nickbild/luminaphone/schematic/schematic.kicad_sch

## KiCad design schematic/schematic.kicad_sch (2025-05-27)

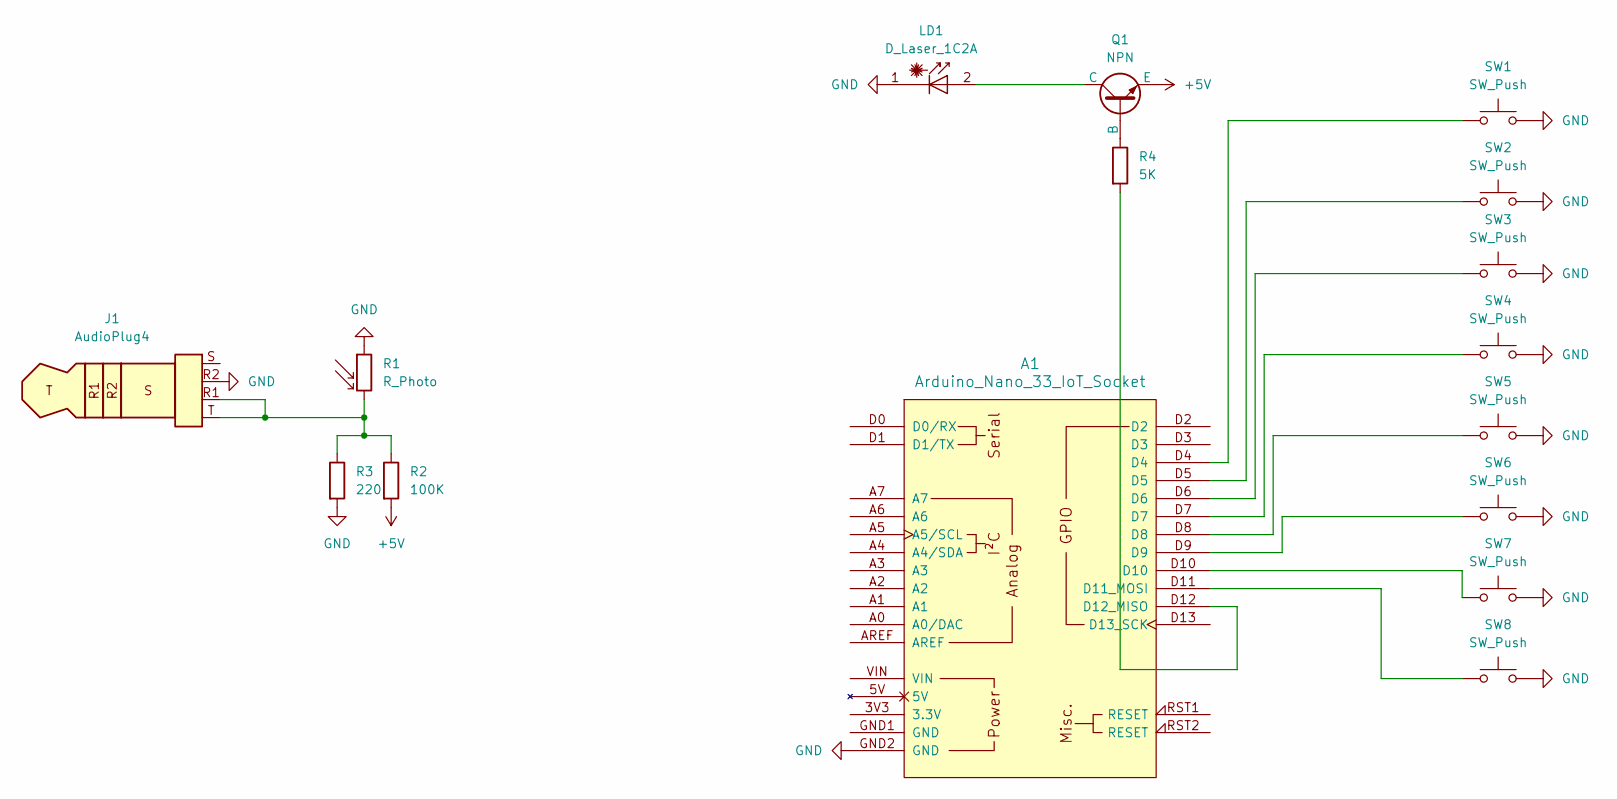
[picture p10: schematic schematic.kicad_sch]

Parts:
A1: Arduino_Nano_33_IoT_Socket
J1: AudioPlug4
LD1: D_Laser_1C2A
Q1: NPN
R1: R_Photo
R2: 100K
R3: 220
R4: 5K
SW1, SW2, SW3, SW4, SW5, SW6, SW7, SW8: SW_Push

Connections:
+5V: Q1.3 (E), R2.2
GND: A1.GND2 (GND), J1.R2, LD1.1 (K), R1.1, R3.2, SW1.2, SW2.2, SW3.2, SW4.2, SW5.2, SW6.2, SW7.2, SW8.2
unnamed: A1.D4, SW1.1
unnamed: A1.D5, SW2.1
unnamed: A1.D6, SW3.1
unnamed: A1.D7, SW4.1
unnamed: A1.D8, SW5.1
unnamed: A1.D9, SW6.1
unnamed: A1.D10, SW7.1
unnamed: A1.D11 (D11_MOSI), SW8.1
unnamed: A1.D12 (D12_MISO), R4.2
unnamed: J1.R1, J1.T, R1.2, R2.1, R3.1
unnamed: LD1.2 (A), Q1.1 (C)
unnamed: Q1.2 (B), R4.1
